mkulesh/stm32DigitalClock/images/mcu_board1.jpg

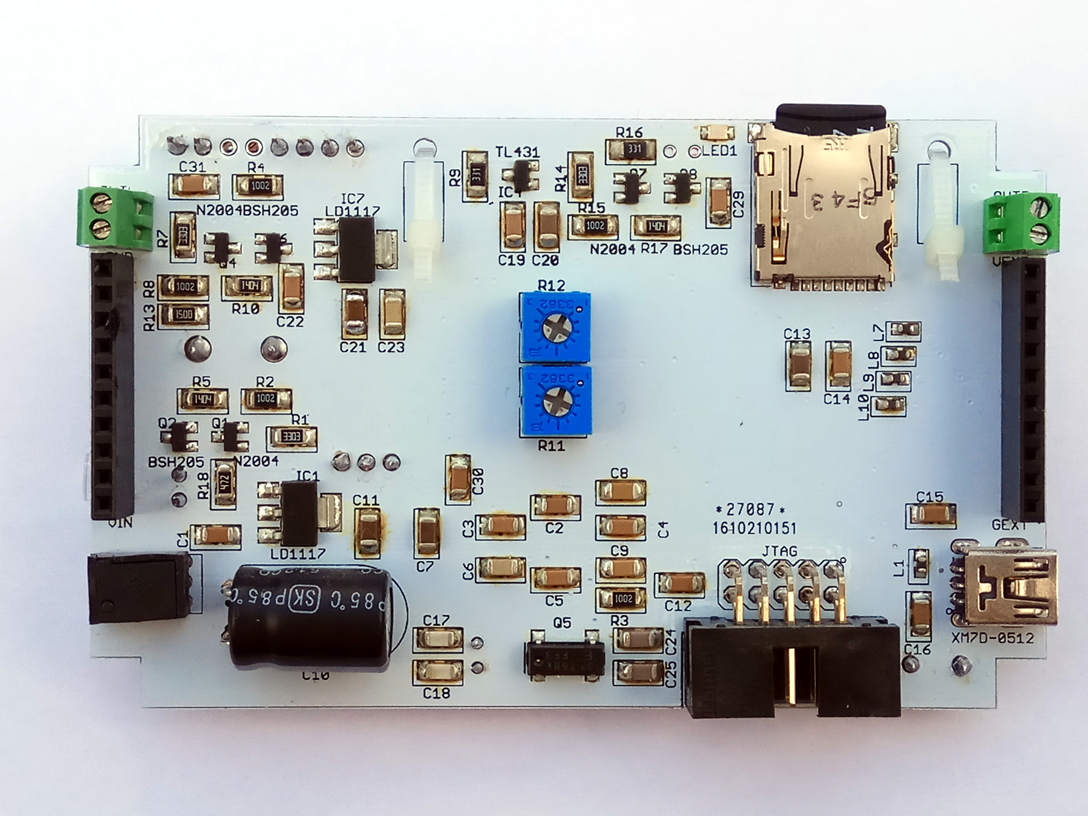
images/mcu_board1.jpg
