mkulesh/stm32DigitalClock/src/src/StmPlusPlus/StmPlusPlus.h

/*******************************************************************************
 * StmPlusPlus: object-oriented library implementing device drivers for 
 * STM32F3 and STM32F4 MCU
 * *****************************************************************************
 * Copyright (C) 2016-2017 Mikhail Kulesh
 * 
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
 * You should have received a copy of the GNU General Public License
 * along with this program.  If not, see <http://www.gnu.org/licenses/>.
 ******************************************************************************/

#ifndef STMPLUSPLUS_H_
#define STMPLUSPLUS_H_

// TODO:
// 1. Change all types to genetic types (aka int instead of in16_t)
// 2. Compile with maximal level of warning check
// 3. Compile with maximal optimization level
// 4. Introduce enumeration for HAL constants used as input parameters

#ifdef STM32F3
#include "stm32f3xx.h"
#include "stm32f3xx_hal_gpio.h"
#include "stm32f3xx_hal_uart.h"
#include "stm32f3xx_hal_tim.h"
#include "stm32f3xx_hal_rcc.h"
#include "stm32f3xx_hal_rcc_ex.h"
#include "stm32f3xx_hal_adc.h"
#endif

#ifdef STM32F4
#include "stm32f4xx.h"
#include "stm32f4xx_hal_gpio.h"
#include "stm32f4xx_hal_uart.h"
#include "stm32f4xx_hal_tim.h"
#include "stm32f4xx_hal_rcc.h"
#include "stm32f4xx_hal_rtc_ex.h"
#include "stm32f4xx_hal_adc.h"
#endif

#include <functional>
#include <ctime>

namespace StmPlusPlus {

/**
 * @brief Additional time types and limits
 */
typedef int32_t duration_sec;
typedef uint64_t time_ms;
typedef int64_t duration_ms;

typedef std::pair<uint32_t, uint32_t> InterruptPriority;

#define INFINITY_SEC __UINT32_MAX__
#define INFINITY_TIME __UINT64_MAX__
#define FIRST_CALENDAR_YEAR 1900

/**
 * @brief Useful primitives
 */
#define lowByte(x)                        ((uint8_t)((x) & 0xFF))
#define highByte(x)                       ((uint8_t)(((x)>>8) & 0xFF))
#define setBitToTrue(uInt8Val, bitNr)   (uInt8Val |= (1 << bitNr))
#define setBitToFalse(uInt8Val, bitNr)  (uInt8Val &= ~(1 << bitNr))

typedef union
{
    uint16_t word;
    struct
    {
        uint8_t low;
        uint8_t high;
    } bytes;
} WordToBytes;


/**
 * @brief Static class collecting helper methods for general system settings.
 */
class System
{

private:

    static uint32_t externalOscillatorFreq;
    static uint32_t mcuFreq;

public:

    enum class RtcType
    {
        RTC_NONE = 0,
        RTC_INT = 1,
        RTC_EXT = 2
    };

    static uint32_t getExternalOscillatorFreq ()
    {
        return externalOscillatorFreq;
    }

    static uint32_t getMcuFreq ()
    {
        return mcuFreq;
    }

    static void setClock (uint32_t pllDiv, uint32_t pllMUL, uint32_t FLatency, RtcType rtcType, int32_t msAdjustment = 0);

};

/**
 * @brief Base IO port class.
 */
class IOPort
{
public:

    /**
     * @brief Enumeration collecting port names.
     *
     * The port name will be used in the constructor in order to set-up the pointers to the port
     * registers.
     */
    enum PortName
    {
        A = 0,
        B = 1,
        C = 2,
        D = 3,
        F = 4
    };

    /**
     * @brief Default constructor.
     */
    IOPort (PortName name,
            uint32_t mode,
            uint32_t pull = GPIO_NOPULL,
            uint32_t speed = GPIO_SPEED_HIGH,
            uint32_t pin = GPIO_PIN_All,
            bool callInit = true);

    /**
     * @brief Specifies the operating mode for the selected pins.
     */
    inline void setMode (uint32_t mode)
    {
        gpioParameters.Mode  = mode;
        HAL_GPIO_Init(port, &gpioParameters);
    }

    /**
     * @brief Specifies the Pull-up or Pull-Down activation for the selected pins.
     */
    inline void setPull (uint32_t pull)
    {
        gpioParameters.Pull  = pull;
        HAL_GPIO_Init(port, &gpioParameters);
    }

    /**
     * @brief Specifies the speed for the selected pins.
     */
    inline void setSpeed (uint32_t speed)
    {
        gpioParameters.Speed  = speed;
        HAL_GPIO_Init(port, &gpioParameters);
    }

    /**
     * @brief Peripheral to be connected to the selected pins.
     */
    inline void setAlternate (uint32_t alternate)
    {
        gpioParameters.Alternate  = alternate;
        HAL_GPIO_Init(port, &gpioParameters);
    }

    /**
     * @brief Lock GPIO Pins configuration registers.
     */
    inline void lock ()
    {
        HAL_GPIO_LockPin(port, gpioParameters.Pin);
    }

    /**
     * @brief  Set the selected data port bit.
     *
     * @note   This function uses GPIOx_BSRR and GPIOx_BRR registers to allow atomic read/modify
     *         accesses. In this way, there is no risk of an IRQ occurring between
     *         the read and the modify access.
     */
    inline void setHigh ()
    {
        HAL_GPIO_WritePin(port, gpioParameters.Pin, GPIO_PIN_SET);
    }

    /**
     * @brief  Clear the selected data port bit.
     *
     * @note   This function uses GPIOx_BSRR and GPIOx_BRR registers to allow atomic read/modify
     *         accesses. In this way, there is no risk of an IRQ occurring between
     *         the read and the modify access.
     */
    inline void setLow ()
    {
        HAL_GPIO_WritePin(port, gpioParameters.Pin, GPIO_PIN_RESET);
    }

    /**
     * @brief Toggle the specified GPIO pin.
     */
    inline void toggle ()
    {
        HAL_GPIO_TogglePin(port, gpioParameters.Pin);
    }

    /**
     * @brief Write the given integer into the GPIO port output data register.
     */
    inline void putInt (uint32_t val)
    {
        port->ODR = val;
    }

    /**
     * @brief Returns the value from GPIO port input data register.
     */
    inline uint32_t getInt ()
    {
        return port->IDR;
    }

protected:

    /**
     * @brief Pointer to the port registers.
     */
    GPIO_TypeDef * port;

    /**
     * @brief Current port parameters.
     */
    GPIO_InitTypeDef gpioParameters;
};


/**
 * @brief Class that describes a single port pin.
 */
class IOPin : public IOPort
{
public:

    /**
     * @brief Default constructor.
     */
    IOPin (PortName name, uint32_t pin, uint32_t mode, uint32_t pull = GPIO_NOPULL, uint32_t speed = GPIO_SPEED_HIGH, bool callInit = true, bool value = false):
        IOPort(name, mode, pull, speed, pin, callInit)
    {
        HAL_GPIO_WritePin(port, gpioParameters.Pin, (GPIO_PinState)value);
    }

    /**
     * @brief Set or clear the selected data port bit.
     *
     * @note   This function uses GPIOx_BSRR and GPIOx_BRR registers to allow atomic read/modify
     *         accesses. In this way, there is no risk of an IRQ occurring between
     *         the read and the modify access.
     */
    inline void putBit (bool value)
    {
        HAL_GPIO_WritePin(port, gpioParameters.Pin, (GPIO_PinState)value);
    }

    /**
     * @brief Return the current value of the pin.
     */
    inline bool getBit () const
    {
        return (bool)HAL_GPIO_ReadPin(port, gpioParameters.Pin);
    }

    /**
     * @brief Activate microcontroller clock output (MCO) for this pin.
     */
    void activateClockOutput (uint32_t source, uint32_t div = RCC_MCODIV_1);
};


/**
 * @brief Class that implements UART interface.
 */
class Usart : public IOPort
{
public:

    enum DeviceName
    {
        USART_1 = 0,
        USART_2 = 1
    };

    /**
     * @brief Default constructor.
     */
    Usart (DeviceName device, PortName name, uint32_t txPin, uint32_t rxPin);

    /**
     * @brief Open transmission session with given parameters.
     */
    HAL_StatusTypeDef start (uint32_t mode,
                             uint32_t baudRate,
                             uint32_t wordLength = UART_WORDLENGTH_8B,
                             uint32_t stopBits = UART_STOPBITS_1,
                             uint32_t parity = UART_PARITY_NONE);

    /**
     * @brief Close the transmission session.
     */
    HAL_StatusTypeDef stop ();

    /**
     * @brief Send an amount of data in blocking mode.
     */
    HAL_StatusTypeDef transmit (const char * buffer);

private:

    UART_HandleTypeDef usartParameters;
    std::function<void()> enableClock, disableClock;
};


#define IS_USART_DEBUG_ACTIVE() (UsartLogger::getInstance() != NULL)

#define USART_DEBUG(text) {\
    if (IS_USART_DEBUG_ACTIVE())\
    {\
        UsartLogger::getStream() << USART_DEBUG_MODULE << text << UsartLogger::ENDL;\
    }}


/**
 * @brief Class implementing USART logger.
 */
class UsartLogger : public Usart
{
public:

    enum Manupulator
    {
        ENDL = 0
    };

    /**
     * @brief Default constructor.
     */
    UsartLogger (DeviceName device, PortName name, uint32_t txPin, uint32_t rxPin, uint32_t _baudRate);

    static UsartLogger * getInstance ()
    {
        return instance;
    }

    static UsartLogger & getStream ()
    {
        return *instance;
    }

    inline void initInstance ()
    {
        instance = this;
        start(UART_MODE_TX, baudRate, UART_WORDLENGTH_8B, UART_STOPBITS_1, UART_PARITY_NONE);
    }

    inline void clearInstance ()
    {
        stop();
        instance = NULL;
    }

    UsartLogger & operator << (const char * buffer);

    UsartLogger & operator << (int n);

    UsartLogger & operator << (Manupulator m);

private:

    static UsartLogger * instance;
    uint32_t baudRate;
};


/**
 * @brief Class that implements timer interface.
 */
class Timer
{
public:

    class EventHandler
    {
    public:

        virtual void onTimerUpdate (const Timer *) =0;
    };


    /**
     * @brief Enumeration collecting timer names.
     */
    enum TimerName
    {
        TIM_1 =  0,
        TIM_2 =  1,
        TIM_3 =  2,
        TIM_4 =  3,
        TIM_5 =  4,
        TIM_6 =  5,
        TIM_7 =  6,
        TIM_8 =  7,
        TIM_9 =  8,
        TIM_10 = 9,
        TIM_11 = 10,
        TIM_12 = 11,
        TIM_13 = 12,
        TIM_14 = 13,
        TIM_15 = 14,
        TIM_16 = 15,
        TIM_17 = 16
    };

    /**
     * @brief Default constructor.
     */
    Timer (TimerName timerName, IRQn_Type _irqName = SysTick_IRQn);

    inline TIM_HandleTypeDef * getTimerParameters ()
    {
        return &timerParameters;
    }

    inline uint32_t getValue () const
    {
        return __HAL_TIM_GET_COUNTER(&timerParameters);
    }

    inline void reset ()
    {
        __HAL_TIM_SET_COUNTER(&timerParameters, 0);
    }

    void setPrescaler (uint32_t prescaler);

    HAL_StatusTypeDef start (uint32_t counterMode,
                             uint32_t prescaler,
                             uint32_t period,
                             uint32_t clockDivision = TIM_CLOCKDIVISION_DIV1,
                             uint32_t repetitionCounter = 1);
    void startInterrupt (const InterruptPriority & prio, EventHandler * _handler = NULL);

    inline void stopInterrupt ()
    {
        HAL_NVIC_DisableIRQ(irqName);
    }

    void processInterrupt () const;

    HAL_StatusTypeDef stop ();

private:

    EventHandler * handler;
    IRQn_Type irqName;
    TIM_HandleTypeDef timerParameters;
};


/**
 * @brief Class that implements real-time clock.
 */
class RealTimeClock
{
public:

    class EventHandler
    {
    public:

        virtual void onRtcWakeUp () =0;
    };

    /**
     * @brief Default constructor.
     */
    RealTimeClock ();

    inline int32_t getErrorMs () const
    {
        return errorMs;
    }

    inline time_ms getTimeMillisec () const
    {
        return timeMillisec;
    }

    inline time_t getTimeSec () const
    {
        return timeSec;
    }

    void setTimeSec (time_t sec)
    {
        timeSec = sec;
        timeMillisec = (duration_ms)sec * 1000L;
    }

    HAL_StatusTypeDef start (uint32_t counterMode, uint32_t prescaler, const InterruptPriority & prio, RealTimeClock::EventHandler * _handler = NULL);

    void onMilliSecondInterrupt ();
    void onSecondInterrupt ();

    void stop ();

private:

    EventHandler * handler;
    RTC_HandleTypeDef rtcParameters;
    RTC_TimeTypeDef timeParameters;
    RTC_DateTypeDef dateParameters;

    // These variables are modified from interrupt service routine, therefore declare them as volatile
    volatile uint32_t syncMs1, syncMs2;
    volatile int32_t errorMs;
    volatile time_ms timeMillisec; // current time (in milliseconds)
    volatile time_t timeSec; // current time (in seconds)
};


/**
 * @brief Class that implements SPI interface.
 */
class Spi
{
public:

    const uint32_t TIMEOUT = 5000;

    enum DeviceName
    {
        SPI_1 = 0,
        SPI_2 = 1,
        SPI_3 = 2,
    };

    /**
     * @brief Default constructor.
     */
    Spi (DeviceName _device,
         IOPort::PortName sckPort, uint32_t sckPin,
         IOPort::PortName misoPort, uint32_t misoPin,
         IOPort::PortName mosiPort, uint32_t mosiPin,
         uint32_t pull = GPIO_NOPULL);

    HAL_StatusTypeDef start (uint32_t direction, uint32_t prescaler, uint32_t dataSize = SPI_DATASIZE_8BIT, uint32_t CLKPhase = SPI_PHASE_1EDGE);

    HAL_StatusTypeDef stop ();

    inline void putChar (uint8_t data)
    {
        /* Transmit data in 8 Bit mode */
        spiParams.Instance->DR = data;
        while (!__HAL_SPI_GET_FLAG(hspi, SPI_FLAG_TXE));
    }

    inline void putInt (uint16_t data)
    {
        /* Transmit data in 16 Bit mode */
        spiParams.Instance->DR = data;
        while (!__HAL_SPI_GET_FLAG(hspi, SPI_FLAG_TXE));
    }

    inline HAL_StatusTypeDef writeBuffer (uint8_t *pData, uint16_t pSize)
    {
        return HAL_SPI_Transmit(hspi, pData, pSize, TIMEOUT);
    }

private:

    DeviceName device;
    IOPin sck, miso, mosi;
    SPI_HandleTypeDef *hspi;
    SPI_HandleTypeDef spiParams;
    std::function<void()> enableClock, disableClock;

};


/**
 * @brief Class that implements a periodical event with a given delay
 */
class PeriodicalEvent
{
private:

    const RealTimeClock & rtc;
    time_ms lastEventTime, delay;
    long maxOccurrence, occurred;

public:

    PeriodicalEvent (const RealTimeClock & _rtc, time_ms _delay, long _maxOccurrence = -1);
    void resetTime ();
    bool isOccured ();
};


/**
 * @brief Class that implements analog-to-digit converter
 */
class AnalogToDigitConverter : public IOPin
{
public:

    const uint32_t INVALID_VALUE = __UINT32_MAX__;

    enum DeviceName
    {
        ADC_1 = 0,
        ADC_2 = 1,
        ADC_3 = 2,
    };

    AnalogToDigitConverter (PortName name, uint32_t pin, DeviceName _device, uint32_t channel, float _vRef);

    HAL_StatusTypeDef start ();
    HAL_StatusTypeDef stop ();
    uint32_t getValue ();
    float getVoltage ();

private:

    DeviceName device;
    ADC_HandleTypeDef * hadc;
    ADC_HandleTypeDef adcParams;
    ADC_ChannelConfTypeDef adcChannel;
    float vRef;
    std::function<void()> enableClock, disableClock;
};

} // end namespace
#endif
