mkulesh/stm32DigitalClock/src/src/Screens.cpp

/*******************************************************************************
 * stm32DigitalClock - a digital clock based on STM32F405 MCU
 * *****************************************************************************
 * Copyright (C) 2016-2017 Mikhail Kulesh
 * 
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
 * You should have received a copy of the GNU General Public License
 * along with this program.  If not, see <http://www.gnu.org/licenses/>.
 ******************************************************************************/

#include "Screens.h"

#include <cstdio>
#include <cstring>

/************************************************************************
 * Common functions and constants
 ************************************************************************/

#define CHAR_SETTINGS 0b11111100
#define CHAR_ALARM 0b10010011
#define CHAR_DEGREE 0b11110010

static const char * emptyString = "      ";
static const char * dayNames[7] = {"So", "Mo", "Di", "Mi", "Do", "Fr", "Sa"};
static const char dcfSymbols[6] = {' ', 'e', '+', '-', 0b00010101, 'X'};

unsigned char cicleIncrement (unsigned char val, int s, unsigned char min, unsigned char max)
{
    unsigned char ret = val;    
    if (s > 0 && ret == max)
    {
        ret = min;
    }
    else if (s < 0 && ret == min)
    {
        ret = max;
    }
    else
    {
        ret += s;
    }
    return ret;
}

/************************************************************************
 * Class HomeScreen
 ************************************************************************/
void HomeScreen::fillLine (int line, const DisplayDataProvider * dataProvider, char * dest)
{
    const ::tm & dayTime = dataProvider->getDayTime();
    if (line == 0)
    {
        sprintf(dest, "%c %02d.%02d.%04d %2s ",
            dcfSymbols[(size_t)dataProvider->getDcfState()],
            dayTime.tm_mday, 
            dayTime.tm_mon + 1, 
            dayTime.tm_year + FIRST_CALENDAR_YEAR,
            dayNames[dayTime.tm_wday]);
    }
    else
    {
        sprintf(dest, "%c %02d:%02d:%02d %2d%cC ",
            (dataProvider->isAlarmActive()? CHAR_ALARM : ' '),
            dayTime.tm_hour, 
            dayTime.tm_min, 
            dayTime.tm_sec,
            (int)(dataProvider->getTemperature()),
            CHAR_DEGREE);
    }
}

/************************************************************************
 * Class TimeSetting
 ************************************************************************/
const unsigned char TimeSetting::elementPos[6][3] = {
    {1, 0, 2}, // TS_DAY
    {4, 0, 2}, // TS_MONTH
    {7, 0, 4}, // TS_YEAR
    {1, 1, 2}, // TS_HOUR
    {4, 1, 2}, // TS_MIN
    {7, 1, 2}  // TS_SEC
};

void TimeSetting::setNext ()
{
    activeElement = (activeElement == TS_SEC)? TS_DAY : (Element)((int)activeElement + 1);
}

void TimeSetting::fillLine (int line, const DisplayDataProvider * dataProvider, char * dest)
{
    if (line == 0)
    {
        sprintf(dest, "%c%02d.%02d.%04d  %2s", CHAR_SETTINGS,
            dataProvider->getDayTime().tm_mday, 
            dataProvider->getDayTime().tm_mon + 1, 
            dataProvider->getDayTime().tm_year + FIRST_CALENDAR_YEAR,
            dayNames[dataProvider->getDayTime().tm_wday]);
    }
    else
    {
        sprintf(dest, " %02d:%02d:%02d", 
            dataProvider->getDayTime().tm_hour, 
            dataProvider->getDayTime().tm_min, 
            dataProvider->getDayTime().tm_sec);
    }
    if (!dataProvider->isActiveElementVisible() && elementPos[activeElement][1] == line)
    {
        strncpy(&dest[elementPos[activeElement][0]], emptyString, elementPos[activeElement][2]);
    }
}

void TimeSetting::modifyValue (::tm & dayTime, int s)
{
    switch (activeElement)
    {
        case TimeSetting::TS_DAY: 
            dayTime.tm_mday += s; 
            break;
        case TimeSetting::TS_MONTH:
            if (s < 0 && dayTime.tm_mon == (int)Months::JANUARY)
            {
                dayTime.tm_mon = (int)Months::DECEMBER;
                dayTime.tm_year--;
            }
            else if (s > 0 && dayTime.tm_mon == (int)Months::DECEMBER)
            {
                dayTime.tm_mon = (int)Months::JANUARY;
                ++dayTime.tm_year;
            }
            else
            {
                dayTime.tm_mon += s;
            }
            break;
        case TimeSetting::TS_YEAR: 
            dayTime.tm_year += s; 
            break;
        case TimeSetting::TS_HOUR: 
            dayTime.tm_hour += s; 
            break;
        case TimeSetting::TS_MIN: 
            dayTime.tm_min += s; 
            break;
        case TimeSetting::TS_SEC: 
            dayTime.tm_sec += s; 
            break;
    }
}

/************************************************************************
 * Class BrightnessSetting
 ************************************************************************/
const unsigned char BrightnessSetting::elementPos[2][3] = {
    {1, 1, 4}, // BS_MODE
    {6, 1, 3}  // BS_MAN_VALUE
};

BrightnessSetting::BrightnessSetting (Config & _config):
    config(_config),
    activeElement(BS_MODE)
{
    // empty
}

void BrightnessSetting::setFirst ()
{
    activeElement = BS_MODE;
}

void BrightnessSetting::setNext ()
{
    if (config.getBrightness().isManual)
    {
        activeElement = (activeElement == BS_MODE)? BS_MAN_VALUE : BS_MODE;
    }
    else
    {
        activeElement = BS_MODE;
    }
}

void BrightnessSetting::fillLine (int line, const DisplayDataProvider * dataProvider, char * dest)
{
    if (line == 0)
    {
        sprintf(dest, "%cBeleuchtung:", CHAR_SETTINGS);
    }
    else
    {
        const Config::Brightness & data = config.getBrightness();
        if (data.isManual)
        {
            sprintf(dest, " MAN: %3d%% ", data.manValue);
        }
        else
        {
            sprintf(dest, " AUTO: %3d%%", dataProvider->getBrightnessValue());
        }
        if (!dataProvider->isActiveElementVisible())
        {
            strncpy(&dest[elementPos[activeElement][0]], emptyString, elementPos[activeElement][2]);
        }
    }
}

void BrightnessSetting::modifyValue (int s)
{
    const Config::Brightness & data = config.getBrightness();
    if (activeElement == BS_MODE)
    {
        config.setBrightnessManual(!data.isManual);
    }
    else
    {
        config.setBrightnessManValue(cicleIncrement(data.manValue, s, 0, 100));
    }
}

/************************************************************************
 * Class AlarmSetting
 ************************************************************************/
const unsigned char AlarmSetting::elementPos[10][3] = {
    { 5, 0, 3}, // AS_ACTIVE
    { 9, 0, 2}, // AS_HOUR
    {12, 0, 2}, // AS_MIN
    { 1, 1, 1}, // AS_DAY1
    { 3, 1, 1}, // AS_DAY2
    { 5, 1, 1}, // AS_DAY3
    { 7, 1, 1}, // AS_DAY4
    { 9, 1, 1}, // AS_DAY5
    {11, 1, 1}, // AS_DAY6
    {13, 1, 1}  // AS_DAY7
};
const char * AlarmSetting::activeString[2] = {"AUS", " AN"};

AlarmSetting::AlarmSetting (size_t _number, Config & _config):
    config(_config),
    activeElement(AS_ACTIVE),
    number(_number)
{
    // empty
}

void AlarmSetting::setFirst ()
{
    activeElement = AS_ACTIVE;
}

void AlarmSetting::setNext ()
{
    activeElement = (activeElement == AS_DAY7)? AS_ACTIVE : (Element)((int)activeElement + 1);
}

void AlarmSetting::fillLine (int line, const DisplayDataProvider * dataProvider, char * dest)
{
    const Config::Alarm & data = config.getAlarm(number);
    if (line == 0)
    {
        sprintf(dest, "%cW%d: %3s %02d:%02d", 
            CHAR_SETTINGS, number + 1, activeString[data.isActive], data.hour, data.min);
    }
    else
    {
        ::memset(dest, ' ', 16);
        for (size_t i = 0; i < 7; ++i)
        {
            dest[elementPos[i + 3][0]] = data.days[i]? dayNames[i][0] : '.';
        }
    }
    if (!dataProvider->isActiveElementVisible() && elementPos[activeElement][1] == line)
    {
        strncpy(&dest[elementPos[activeElement][0]], emptyString, elementPos[activeElement][2]);
    }
}

void AlarmSetting::modifyValue (int s)
{
    const Config::Alarm & data = config.getAlarm(number);
    switch (activeElement)
    {
    case AS_ACTIVE:
        config.setAlarmActive(number, !data.isActive);
        break;
    case AS_HOUR:
        config.setAlarmHour(number, cicleIncrement(data.hour, s, 0, 23));
        break;
    case AS_MIN:
        config.setAlarmMin(number, cicleIncrement(data.min, s, 0, 59));
        break;
    case AS_DAY1: case AS_DAY2: case AS_DAY3: case AS_DAY4: case AS_DAY5: case AS_DAY6: case AS_DAY7:
        {
            size_t dayNr = activeElement - 3;
            config.setAlarmDay(number, dayNr, !data.days[dayNr]);
        }
        break;
    }
}
